kndndrj/mouse/firmware-c/drivers/sensors/pmw3360_fw_liftoff.h

#ifndef DRIVER_SENSOR_PMW3360_FW_LIFTOFF_H
#define DRIVER_SENSOR_PMW3360_FW_LIFTOFF_H

#include <stdint.h>

// SROM 0x81
static const uint8_t pmw3360_fw_liftoff[] = {
    0x01, 0x81, 0x01, 0x82, 0x46, 0x27, 0x9e, 0xbe, 0xfe, 0x5f, 0x3c, 0xfa,
    0x76, 0x6e, 0x5e, 0x3e, 0xfe, 0x5f, 0x1d, 0x99, 0x91, 0xa0, 0xc2, 0x06,
    0x8e, 0x9e, 0x9f, 0xbc, 0xdb, 0x34, 0xea, 0x56, 0x0f, 0x9c, 0x9b, 0xb4,
    0xcb, 0x14, 0x8b, 0x75, 0x68, 0x33, 0xc5, 0x08, 0x73, 0x45, 0xe9, 0x50,
    0x22, 0xa7, 0xcc, 0xfb, 0x55, 0x28, 0xb3, 0xc5, 0x08, 0x92, 0xa6, 0xaf,
    0xdc, 0x3a, 0xf6, 0x4f, 0x1c, 0x9b, 0xb4, 0xcb, 0x14, 0x8b, 0x94, 0xaf,
    0xd6, 0x2e, 0xde, 0x1f, 0x9d, 0xb8, 0xf2, 0x66, 0x4f, 0xff, 0x7c, 0x7a,
    0x76, 0x6e, 0x5e, 0x3e, 0xdf, 0x1d, 0x99, 0xb0, 0xe2, 0x46, 0x0d, 0x9e,
    0x9b, 0xbc, 0xfa, 0x76, 0x6e, 0x5e, 0x1f, 0x9d, 0x99, 0xb6, 0xe2, 0x25,
    0xcc, 0x1a, 0x97, 0xac, 0xbb, 0xf4, 0x6a, 0x37, 0xcd, 0xf9, 0x70, 0xaa,
    0xa2, 0x04, 0x6f, 0x9d, 0x8c, 0x1a, 0xbc, 0x44, 0x06, 0xad, 0xe7, 0x73,
    0x58, 0x33, 0x3a, 0x89, 0xac, 0xab, 0xe6, 0xf2, 0x59, 0x9c, 0xe4, 0x7f,
    0xe2, 0x94, 0x9f, 0x6e, 0x56, 0x0b, 0x78, 0x79, 0xa8, 0x5e, 0xb5, 0x06,
    0x63, 0x63, 0x6e, 0xb9, 0xf4, 0xf5, 0x64, 0x6d, 0x16, 0x4e, 0x35, 0xe2,
    0x0c, 0x55, 0xe6, 0x20, 0xd5, 0xc6, 0xab, 0x41, 0xd1, 0x51, 0xe6, 0xf6,
    0x4b, 0x4c, 0xf5, 0x7d, 0x01, 0x56, 0x36, 0xcb, 0xad, 0x16, 0x3e, 0x8d,
    0x20, 0x44, 0x0e, 0x27, 0x02, 0x57, 0x5d, 0x75, 0xa7, 0xe9, 0x69, 0x55,
    0x8a, 0xd8, 0x10, 0x35, 0x07, 0x8f, 0x07, 0xca, 0x7c, 0x7a, 0x73, 0xc5,
    0x8b, 0xe0, 0x35, 0xe7, 0xd1, 0x41, 0x5e, 0xd5, 0x5e, 0x5f, 0x09, 0xc7,
    0x0a, 0x06, 0x6a, 0xfe, 0xea, 0xdf, 0xb2, 0x4e, 0xbb, 0xbd, 0xfe, 0x82,
    0x7e, 0xf6, 0x46, 0x32, 0x3e, 0xe0, 0xac, 0xb6, 0x09, 0x89, 0x94, 0xd3,
    0xe8, 0xfd, 0xf2, 0x4e, 0x3d, 0x9e, 0xc1, 0xbd, 0x86, 0x95, 0x11, 0xd7,
    0x85, 0x80, 0xda, 0x95, 0x86, 0x8d, 0xc9, 0xb3, 0xcb, 0xf4, 0x1a, 0x15,
    0x94, 0x6c, 0x0b, 0x37, 0xcb, 0xa6, 0x9f, 0x1f, 0x87, 0xc0, 0xec, 0xe4,
    0x3a, 0x34, 0xf1, 0x4f, 0xdc, 0xd8, 0xcb, 0x6e, 0x5d, 0xb4, 0xb1, 0x9b,
    0xd4, 0xa6, 0x28, 0x0e, 0xe1, 0x1f, 0x95, 0x6c, 0x4e, 0x76, 0x00, 0x42,
    0x85, 0xdd, 0x0f, 0x7e, 0x9a, 0xc6, 0xac, 0xed, 0x0c, 0xea, 0xf4, 0x3d,
    0x2a, 0x16, 0x0e, 0xee, 0xfc, 0x35, 0x2b, 0x11, 0x69, 0x01, 0x03, 0x3f,
    0x34, 0x07, 0x97, 0xbd, 0x3b, 0xac, 0x16, 0x48, 0xfe, 0x0e, 0x1d, 0xc0,
    0xcc, 0xf8, 0x96, 0xbf, 0x3f, 0xbd, 0x65, 0x9f, 0x70, 0xfa, 0xe7, 0xcb,
    0xed, 0xcf, 0x94, 0x33, 0x7e, 0x60, 0x06, 0x49, 0x4d, 0x23, 0x25, 0xed,
    0x00, 0xd5, 0x25, 0x18, 0x9c, 0x69, 0x8c, 0xc0, 0x74, 0x12, 0x65, 0xd0,
    0x39, 0x06, 0xe0, 0xf9, 0x1a, 0x78, 0xd0, 0x65, 0x5f, 0xa9, 0xac, 0x6a,
    0x38, 0x52, 0x0f, 0x6c, 0xaa, 0x72, 0xa3, 0x8e, 0x39, 0x1e, 0x4a, 0x6a,
    0xc7, 0xa9, 0x1a, 0xb3, 0xa5, 0x7e, 0x5b, 0x6c, 0x4f, 0xe8, 0xc2, 0x40,
    0xca, 0xef, 0x0f, 0x1a, 0xb6, 0x56, 0x37, 0x3b, 0x39, 0x52, 0x38, 0xb7,
    0x4e, 0x88, 0x56, 0xef, 0x1a, 0x8a, 0xa0, 0x41, 0x76, 0xa8, 0xd3, 0xa2,
    0x25, 0x13, 0xa5, 0xc4, 0x0e, 0x1e, 0x59, 0xe8, 0xc9, 0x19, 0xb6, 0xb4,
    0x88, 0x86, 0x0b, 0x64, 0x44, 0xaf, 0xe2, 0xbc, 0x8a, 0x91, 0x09, 0xcd,
    0xa7, 0x79, 0xe0, 0x57, 0xd1, 0xd4, 0xe7, 0x00, 0x77, 0x20, 0x27, 0xcc,
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

#endif
