kndndrj/mouse/firmware-c/hal/stm32/f0/usb.c

#include "usb.h"

#include <libopencm3/stm32/rcc.h>
#include <libopencm3/usb/hid.h>
#include <libopencm3/usb/usbd.h>
#include <stdlib.h>

// TODO: make descriptors modular (not tied to libopencm3)

//
// Descriptors
//
struct usb_device_descriptor dev_descr = {
    .bLength = USB_DT_DEVICE_SIZE,
    .bDescriptorType = USB_DT_DEVICE,
    .bcdUSB = 0x0200,
    .bDeviceClass = 0,
    .bDeviceSubClass = 0,
    .bDeviceProtocol = 0,
    .bMaxPacketSize0 = 64,
    .idVendor = 0x0483,
    .idProduct = 0x5710,
    .bcdDevice = 0x0200,
    .iManufacturer = 1,
    .iProduct = 2,
    .iSerialNumber = 3,
    .bNumConfigurations = 1,
};

const uint8_t hid_report_descriptor[] = {
    0x05, 0x01, /* USAGE_PAGE (Generic Desktop)         */
    0x09, 0x02, /* USAGE (Mouse)                        */
    0xa1, 0x01, /* COLLECTION (Application)             */
    0x09, 0x01, /*   USAGE (Pointer)                    */
    0xa1, 0x00, /*   COLLECTION (Physical)              */
    0x05, 0x09, /*     USAGE_PAGE (Button)              */
    0x19, 0x01, /*     USAGE_MINIMUM (Button 1)         */
    0x29, 0x03, /*     USAGE_MAXIMUM (Button 3)         */
    0x15, 0x00, /*     LOGICAL_MINIMUM (0)              */
    0x25, 0x01, /*     LOGICAL_MAXIMUM (1)              */
    0x95, 0x03, /*     REPORT_COUNT (3)                 */
    0x75, 0x01, /*     REPORT_SIZE (1)                  */
    0x81, 0x02, /*     INPUT (Data,Var,Abs)             */
    0x95, 0x01, /*     REPORT_COUNT (1)                 */
    0x75, 0x05, /*     REPORT_SIZE (5)                  */
    0x81, 0x01, /*     INPUT (Cnst,Ary,Abs)             */
    0x05, 0x01, /*     USAGE_PAGE (Generic Desktop)     */
    0x09, 0x30, /*     USAGE (X)                        */
    0x09, 0x31, /*     USAGE (Y)                        */
    0x09, 0x38, /*     USAGE (Wheel)                    */
    0x15, 0x81, /*     LOGICAL_MINIMUM (-127)           */
    0x25, 0x7f, /*     LOGICAL_MAXIMUM (127)            */
    0x75, 0x08, /*     REPORT_SIZE (8)                  */
    0x95, 0x03, /*     REPORT_COUNT (3)                 */
    0x81, 0x06, /*     INPUT (Data,Var,Rel)             */
    0xc0,       /*   END_COLLECTION                     */
    0x09, 0x3c, /*   USAGE (Motion Wakeup)              */
    0x05, 0xff, /*   USAGE_PAGE (Vendor Defined Page 1) */
    0x09, 0x01, /*   USAGE (Vendor Usage 1)             */
    0x15, 0x00, /*   LOGICAL_MINIMUM (0)                */
    0x25, 0x01, /*   LOGICAL_MAXIMUM (1)                */
    0x75, 0x01, /*   REPORT_SIZE (1)                    */
    0x95, 0x02, /*   REPORT_COUNT (2)                   */
    0xb1, 0x22, /*   FEATURE (Data,Var,Abs,NPrf)        */
    0x75, 0x06, /*   REPORT_SIZE (6)                    */
    0x95, 0x01, /*   REPORT_COUNT (1)                   */
    0xb1, 0x01, /*   FEATURE (Cnst,Ary,Abs)             */
    0xc0        /* END_COLLECTION                       */
};

const struct {
  struct usb_hid_descriptor hid_descriptor;
  struct {
    uint8_t bReportDescriptorType;
    uint16_t wDescriptorLength;
  } __attribute__((packed)) hid_report;
} __attribute__((packed))
hid_function = {.hid_descriptor =
                    {
                        .bLength = sizeof(hid_function),
                        .bDescriptorType = USB_DT_HID,
                        .bcdHID = 0x0100,
                        .bCountryCode = 0,
                        .bNumDescriptors = 1,
                    },
                .hid_report = {
                    .bReportDescriptorType = USB_DT_REPORT,
                    .wDescriptorLength = sizeof(hid_report_descriptor),
                }};

const struct usb_endpoint_descriptor hid_endpoint = {
    .bLength = USB_DT_ENDPOINT_SIZE,
    .bDescriptorType = USB_DT_ENDPOINT,
    .bEndpointAddress = 0x81,
    .bmAttributes = USB_ENDPOINT_ATTR_INTERRUPT,
    .wMaxPacketSize = 4,
    .bInterval = 1,
};

const struct usb_interface_descriptor hid_iface = {
    .bLength = USB_DT_INTERFACE_SIZE,
    .bDescriptorType = USB_DT_INTERFACE,
    .bInterfaceNumber = 0,
    .bAlternateSetting = 0,
    .bNumEndpoints = 1,
    .bInterfaceClass = USB_CLASS_HID,
    .bInterfaceSubClass = 1, /* boot */
    .bInterfaceProtocol = 2, /* mouse */
    .iInterface = 0,

    .endpoint = &hid_endpoint,

    .extra = &hid_function,
    .extralen = sizeof(hid_function),
};

const struct usb_interface ifaces[] = {{
    .num_altsetting = 1,
    .altsetting = &hid_iface,
}};

const struct usb_config_descriptor config = {
    .bLength = USB_DT_CONFIGURATION_SIZE,
    .bDescriptorType = USB_DT_CONFIGURATION,
    .wTotalLength = 0,
    .bNumInterfaces = 1,
    .bConfigurationValue = 1,
    .iConfiguration = 0,
    .bmAttributes = 0xC0,
    .bMaxPower = 0x32,

    .interface = ifaces,
};

const char *usb_strings[] = {
    "Mouse Company",
    "HID Demo",
    "DEMO",
};

//
// USB device
//

static enum usbd_request_return_codes hid_control_request(
    usbd_device *dev, struct usb_setup_data *req, uint8_t **buf, uint16_t *len,
    void (**complete)(usbd_device *, struct usb_setup_data *)) {
  (void)complete;
  (void)dev;

  if ((req->bmRequestType != 0x81) ||
      (req->bRequest != USB_REQ_GET_DESCRIPTOR) || (req->wValue != 0x2200))
    return USBD_REQ_NOTSUPP;

  /* Handle the HID report descriptor. */
  *buf = (uint8_t *)hid_report_descriptor;
  *len = sizeof(hid_report_descriptor);

  return USBD_REQ_HANDLED;
}

static void hid_set_config(usbd_device *dev, uint16_t wValue) {
  (void)wValue;
  (void)dev;

  usbd_ep_setup(dev, 0x81, USB_ENDPOINT_ATTR_INTERRUPT, 4, NULL);

  usbd_register_control_callback(
      dev, USB_REQ_TYPE_STANDARD | USB_REQ_TYPE_INTERFACE,
      USB_REQ_TYPE_TYPE | USB_REQ_TYPE_RECIPIENT, hid_control_request);
}

usb_driver_t USB_init(void) {
  // usb device
  static usbd_device *usbd_dev;
  static bool initialised = false;
  if (initialised) {
    return usbd_dev;
  }

  // Buffer to be used for control requests.
  static uint8_t usbd_control_buffer[128];

  // TODO: explicitly define usb pins?
  rcc_periph_clock_enable(RCC_GPIOA);
  rcc_periph_clock_enable(RCC_USB);

  // TODO: make descriptors modular
  usbd_dev =
      usbd_init(&st_usbfs_v2_usb_driver, &dev_descr, &config, usb_strings, 3,
                usbd_control_buffer, sizeof(usbd_control_buffer));

  usbd_register_set_config_callback(usbd_dev, hid_set_config);

  // Reenumeraion done automatically for f0 chips

  initialised = true;

  return usbd_dev;
}

void USB_poll(usb_driver_t driver) { usbd_poll(driver); }

// TODO: make buf modular
void USB_write_packet(usb_driver_t driver, const void *buf) {
  usbd_ep_write_packet(driver, 0x81, buf, 4);
}
