kndndrj/mouse/firmware-rust/mouse-libs/src/pmw3360/registers.rs

#![allow(dead_code)]
pub const PRODUCT_ID: u8 = 0x00;
pub const REVISION_ID: u8 = 0x01;
pub const MOTION: u8 = 0x02;
pub const DELTA_X_L: u8 = 0x03;
pub const DELTA_X_H: u8 = 0x04;
pub const DELTA_Y_L: u8 = 0x05;
pub const DELTA_Y_H: u8 = 0x06;
pub const SQUAL: u8 = 0x07;
pub const RAW_DATA_SUM: u8 = 0x08;
pub const MAXIMUM_RAW_DATA: u8 = 0x09;
pub const MINIMUM_RAW_DATA: u8 = 0x0A;
pub const SHUTTER_LOWER: u8 = 0x0B;
pub const SHUTTER_UPPER: u8 = 0x0C;
pub const CONTROL: u8 = 0x0D;
pub const CONFIG_1: u8 = 0x0F;
pub const CONFIG_2: u8 = 0x10;
pub const ANGLE_TUNE: u8 = 0x11;
pub const FRAME_CAPTURE: u8 = 0x12;
pub const SROM_ENABLE: u8 = 0x13;
pub const RUN_DOWNSHIFT: u8 = 0x14;
pub const REST_1_RATE_LOWER: u8 = 0x15;
pub const REST_1_RATE_UPPER: u8 = 0x16;
pub const REST_1_DOWNSHIFT: u8 = 0x17;
pub const REST_2_RATE_LOWER: u8 = 0x18;
pub const REST_2_RATE_UPPER: u8 = 0x19;
pub const REST_2_DOWNSHIFT: u8 = 0x1A;
pub const REST_3_RATE_LOWER: u8 = 0x1B;
pub const REST_3_RATE_UPPER: u8 = 0x1C;
pub const OBSERVATION: u8 = 0x24;
pub const DATA_OUT_LOWER: u8 = 0x25;
pub const DATA_OUT_UPPER: u8 = 0x26;
pub const RAW_DATA_DUMP: u8 = 0x29;
pub const SROM_ID: u8 = 0x2A;
pub const MIN_SQ_RUN: u8 = 0x2B;
pub const RAW_DATA_THRESHOLD: u8 = 0x2C;
pub const CONFIG_5: u8 = 0x2F;
pub const POWER_UP_RESET: u8 = 0x3A;
pub const SHUTDOWN: u8 = 0x3B;
pub const INVERSE_PRODUCT_ID: u8 = 0x3F;
pub const LIFTCUTOFF_TUNE_3: u8 = 0x41;
pub const ANGLE_SNAP: u8 = 0x42;
pub const LIFTCUTOFF_TUNE_1: u8 = 0x4A;
pub const MOTION_BURST: u8 = 0x50;
pub const LIFTCUTOFF_TUNE_TIMEOUT: u8 = 0x58;
pub const LIFTCUTOFF_TUNE_MIN_LENGTH: u8 = 0x5A;
pub const SROM_LOAD_BURST: u8 = 0x62;
pub const LIFT_CONFIG: u8 = 0x63;
pub const RAW_DATA_BURST: u8 = 0x64;
pub const LIFTCUTOFF_TUNE_2: u8 = 0x65;
